3DGoat/BenchBot/BenchBot CAD/STLs/Y Belt.stl

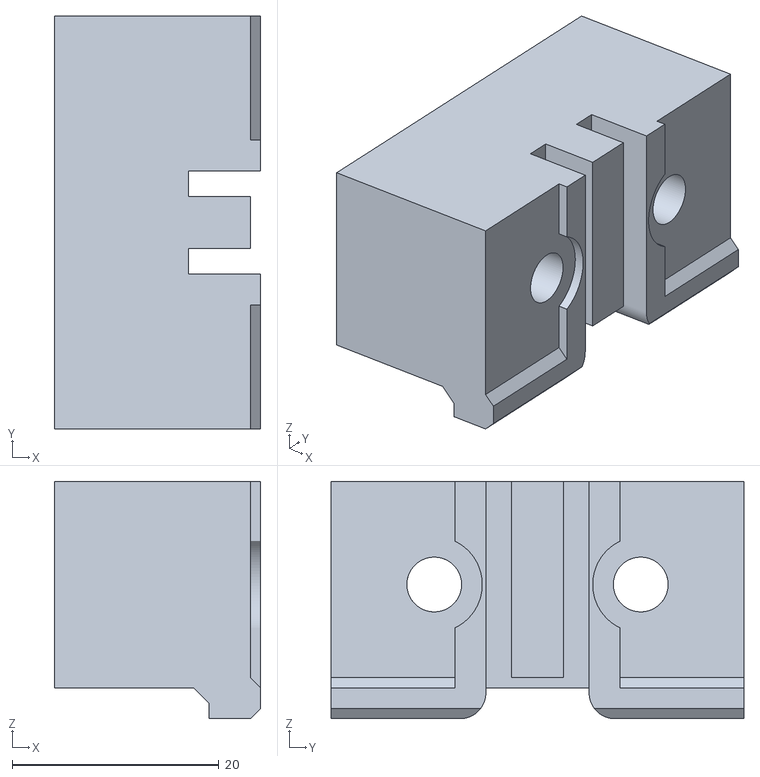
[picture p17: CAD file, 2019-03-17]
BenchBot CAD/STLs/Y Belt.stl
20.0 x 40.0 x 23.0
