3DGoat/BenchBot/BenchBot CAD/STLs/T-Slot Clip.stl

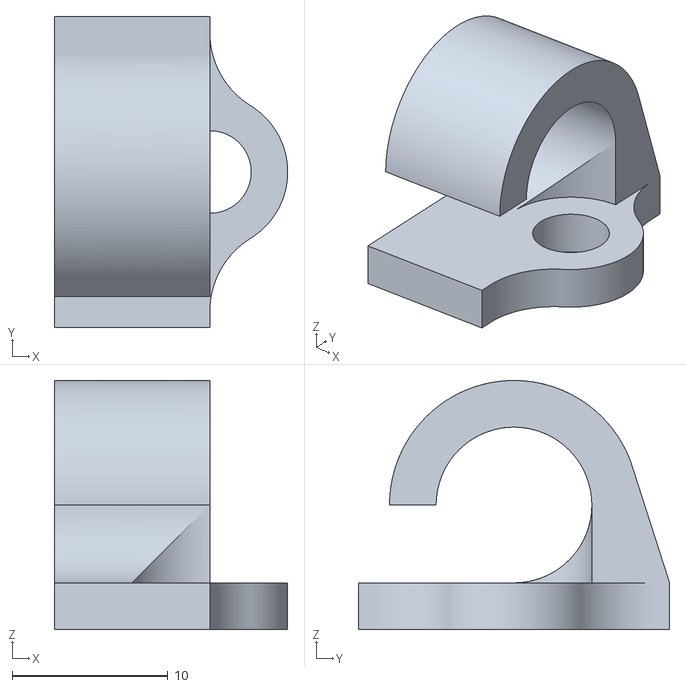
[picture p18: CAD file, 2019-03-17]
BenchBot CAD/STLs/T-Slot Clip.stl
15.0 x 20.0 x 16.0
